qwedus/GGOLCHA_SERVER/.github/assets/wide-black.png

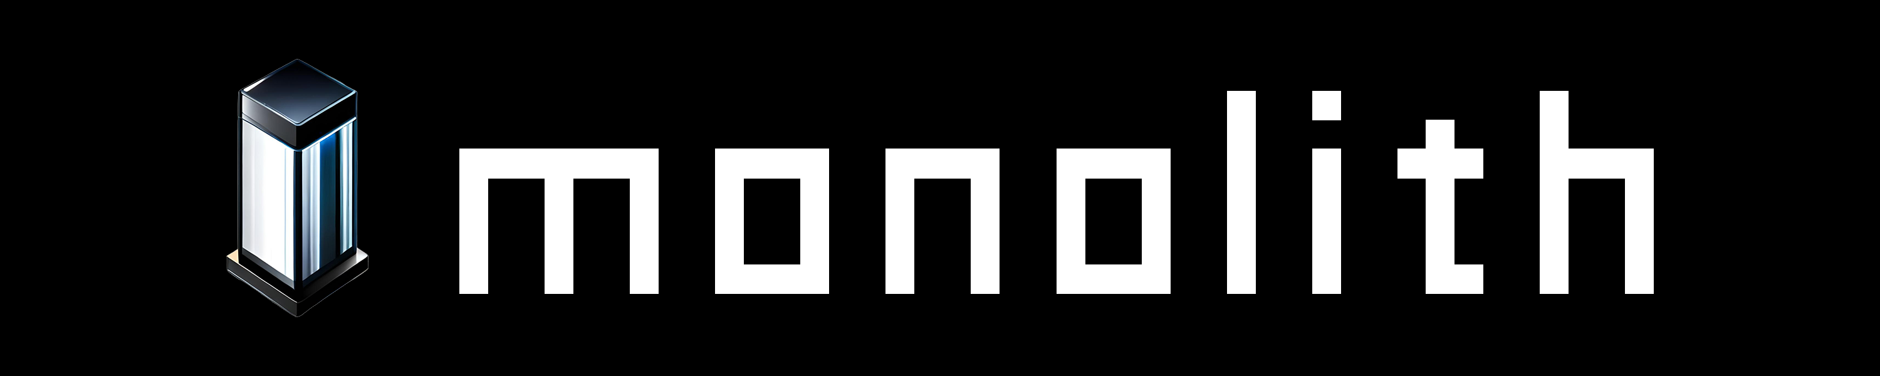
.github/assets/wide-black.png
